fmckeogh/bluefly/controller/build.rs

use std::env;
use std::path::PathBuf;

fn main() {
    // Put the linker script somewhere the linker can find it
    let out = &PathBuf::from(env::var_os("OUT_DIR").unwrap());
    println!("cargo:rustc-link-search={}", out.display());
    println!("cargo:rerun-if-changed=build.rs");
}
